NeuroTinker/NeuroBytes_Touch_Sensor/HARDWARE/copper.png

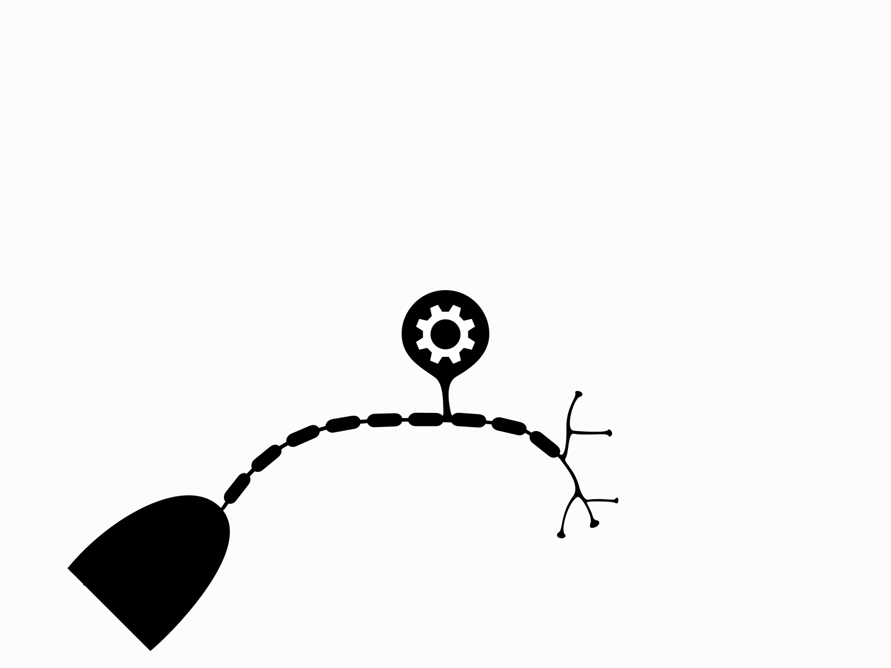
HARDWARE/copper.png
